nicolasdb/GIEP-Arcade-Game-SIM/src/ButtonHandler.h

#pragma once
#include <Arduino.h>
#include <array>
#include "DebugLogger.h"
#include "GameLogic.h"
#include "MCP23017Handler.h"
#include "config.h"

class ButtonHandler {
public:
    static constexpr uint8_t DEBOUNCE_DELAY = 60; // milliseconds

    ButtonHandler(MCP23017Handler& mcpHandler, GameLogic& gameLogic);
    void update();

private:
    MCP23017Handler& _mcpHandler;
    GameLogic& _gameLogic;
    uint8_t _lastMcpStates;
    uint8_t _mcpButtonStates;
    std::array<uint32_t, NUM_MCP_BUTTONS> _lastMcpDebounceTime;
    uint8_t _lastBasinGateState;
    uint8_t _basinGateButtonState;
    uint32_t _lastBasinGateDebounceTime;
    uint8_t _lastDebugState;
    uint8_t _debugButtonState;
    uint32_t _lastDebugDebounceTime;

    void updateMcpButtons(uint32_t now);
    void updateBasinGateButton(uint32_t now);
    void updateDebugButton(uint32_t now);
    void onButtonPressed(uint8_t button);
    void onButtonReleased(uint8_t button);
    void onBasinGateButtonPressed();
    void onBasinGateButtonReleased();
    void onDebugButtonPressed();
};
